ZioGuido/GMLAB_MJU/Arduino/GMLAB_MJU_M61L/velocity_scale.h

#ifndef __VELOCITY_SCALE_
#define __VELOCITY_SCALE_


// Mojo61 v.1.51
const unsigned char VelocityScale[128] =
{
	1, 	// 0
	1, 	// 1
	1, 	// 2
	1, 	// 3
	1, 	// 4
	1, 	// 5
	1, 	// 6
	1, 	// 7
	1, 	// 8
	1, 	// 9
	1, 	// 10
	1, 	// 11
	1, 	// 12
	1, 	// 13
	1, 	// 14
	1, 	// 15
	1, 	// 16
	1, 	// 17
	2, 	// 18
	2, 	// 19
	2, 	// 20
	2, 	// 21
	2, 	// 22
	3, 	// 23
	3, 	// 24
	3, 	// 25
	3, 	// 26
	3, 	// 27
	4, 	// 28
	4, 	// 29
	4, 	// 30
	4, 	// 31
	5, 	// 32
	5, 	// 33
	5, 	// 34
	5, 	// 35
	6, 	// 36
	6, 	// 37
	6, 	// 38
	7, 	// 39
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
};


//////////////////////////////////////////////////////////////////////////////////////////////////////////////////////
// Black keys have a shorter coarse, so the same force applied to a black key produces a higher velocity level
// than a white key, for this reason, before applying any velocity scale, we need to compensate for the black keys.
//////////////////////////////////////////////////////////////////////////////////////////////////////////////////////

// This is y = x^1.35
const unsigned char BlackKeyVelocity[128] =
{
	1,	// 0
	1,	// 1
	1,	// 2
	1,	// 3
	1,	// 4
	1,	// 5
	2,	// 6
	2,	// 7
	3,	// 8
	3,	// 9
	4,	// 10
	4,	// 11
	5,	// 12
	5,	// 13
	6,	// 14
	7,	// 15
	7,	// 16
	8,	// 17
	9,	// 18
	9,	// 19
	10,	// 20
	11,	// 21
	11,	// 22
	12,	// 23
	13,	// 24
	14,	// 25
	14,	// 26
	15,	// 27
	16,	// 28
	17,	// 29
	18,	// 30
	18,	// 31
	19,	// 32
	20,	// 33
	21,	// 34
	22,	// 35
	23,	// 36
	24,	// 37
	24,	// 38
	25,	// 39
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
};

const unsigned char BlackKey_note_num[25] =
{
	37, 39, 42, 44, 46,	// Octave 1
	49, 51, 54, 56, 58,	// Octave 2
	61, 63, 66, 68, 70,	// Octave 3
	73, 75, 78, 80, 82,	// Octave 4
	85, 87, 90, 92, 94,	// Octave 5
};

#endif
